Edzelf/ESP32-Radio/src/oled.h

//***************************************************************************************************
//                                   O L E D . H                                                    *
//***************************************************************************************************
// Driver for SSD1306/SSD1309/SH1106 display                                                        *
//***************************************************************************************************
// 25-02-2021, ES: Correct bug, isSH1106 was always set.                                            *
//***************************************************************************************************
#include <driver/i2c.h>
#include <string.h>

#define OLED_I2C_ADDRESS   0x3C
#define SCREEN_WIDTH        128                    // OLED display width, in pixels
#define SCREEN_HEIGHT        64                    // OLED display height, in pixels

// Color definitions.  OLED only have 2 colors.
#define BLACK   0
#define BLUE    0xFF
#define RED     0xFF
#define GREEN   0
#define CYAN    GREEN | BLUE
#define MAGENTA RED | BLUE
#define YELLOW  RED | GREEN
#define WHITE   RED | GREEN | BLUE

#define OLED_NPAG    8                             // Number of pages (text lines)

// Data to display.  There are TFTSECS sections
struct page_struct
{
  uint8_t   page[128] ;                            // Buffer for one page (8 pixels heigh)
  bool      dirty ;                                // True if modified
} ;
uint8_t     fillbuf[] = { 0, 0, 0, 0 } ;           // To clear 4 bytes of SH1106 RAM

class OLED
{
  public:
    OLED    ( uint8_t sda, uint8_t scl ) ;            // Constructor
    void      clear() ;                               // Clear buffer
    void      display() ;                             // Display buffer
    void      print ( char c ) ;                      // Print a character
    void      print ( const char* str ) ;             // Print a string
    void      setCursor ( uint8_t x, uint8_t y ) ;    // Position the cursor
    void      fillRect ( uint8_t x, uint8_t y,        // Fill a rectangle
                         uint8_t w, uint8_t h,
                         uint8_t color ) ;
    void      drawBitmap ( uint8_t x, uint8_t y,      // Bitmap to display buffer
                           uint8_t* buf,
                           uint8_t w,
                           uint8_t h ) ;        
  private:
    bool                    isSH1106 = false ;        // Display is a SH1106 or not
    bool                    isSSD1309 = false ;       // Display is a SSD1309 or not
    i2c_cmd_handle_t        i2Cchan ;                 // Channel for I2C communication
    struct page_struct*     ssdbuf = NULL ;
    const  uint8_t*         font ;                    // Font to use
    uint8_t                 xchar = 0 ;               // Current cursor position (text)
    uint8_t                 ychar = 0 ;               // Current cursor position (text)
    void                    openI2Cchan() ;           // Open I2C channel
    void                    closeI2Cchan() ;          // Close I2C channel
    void                    wrI2Cchan ( uint8_t b ) ; // Send 1 byte to I2C buffer
} ;


OLED* tft = NULL ;                                    // Object for display

#define TFTSECS 4
scrseg_struct     tftdata[TFTSECS] =                  // Screen divided in 3 segments + 1 overlay
{                                                     // One text line is 8 pixels
  { false, WHITE,   0,  8, "" },                      // 1 top line
  { false, CYAN,    8, 32, "" },                      // 4 lines in the middle
  { false, YELLOW, 40, 22, "" },                      // 3 lines at the bottom, leave room for indicator
  { false, GREEN,  40, 22, "" }                       // 3 lines at the bottom for rotary encoder
} ;

// Various macro's to mimic the ST7735 version of display functions
#define dsp_setRotation()                                          // Use standard landscape format
#define dsp_setTextSize(a)                                         // Set the text size
#define dsp_setTextColor(a)
#define dsp_print(a)            tft->print ( a )                   // Print a string 
#define dsp_println(a)          tft->print ( a ) ; \
                                tft->print ( '\n' )                // Print string plus newline
#define dsp_setCursor(a,b)      tft->setCursor ( a, b )            // Position the cursor
#define dsp_fillRect(a,b,c,d,e) tft->fillRect ( a, b, c, d, e )    // Fill a rectangle
#define dsp_erase()             tft->clear()                       // Clear the screen
#define dsp_getwidth()          128                                // Get width of screen
#define dsp_getheight()         64                                 // Get height of screen
#define dsp_update()            tft->display()                     // Updates to the physical screen
#define dsp_usesSPI()           false                              // Does not use SPI

bool dsp_begin()
{
  
  dbgprint ( "Init OLED, I2C pins %d,%d",
             ini_block.tft_sda_pin,
             ini_block.tft_scl_pin ) ;
  if ( ( ini_block.tft_sda_pin >= 0 ) &&
       ( ini_block.tft_scl_pin >= 0 ) )
  {
    tft = new OLED ( ini_block.tft_sda_pin,
                     ini_block.tft_scl_pin ) ;                    // Create an instant for TFT
  }
  else
  {
    dbgprint ( "Init LCD failed!" ) ;
    
  }
  return ( tft != NULL ) ;
}



// Control byte
#define OLED_CONTROL_BYTE_CMD_SINGLE    0x80
#define OLED_CONTROL_BYTE_CMD_STREAM    0x00
#define OLED_CONTROL_BYTE_DATA_STREAM   0x40

// Fundamental commands (pg.28)
#define OLED_CMD_SET_CONTRAST           0x81    // follow with 0x7F
#define OLED_CMD_DISPLAY_RAM            0xA4
#define OLED_CMD_DISPLAY_ALLON          0xA5
#define OLED_CMD_DISPLAY_NORMAL         0xA6
#define OLED_CMD_DISPLAY_INVERTED       0xA7
#define OLED_CMD_DISPLAY_OFF            0xAE
#define OLED_CMD_DISPLAY_ON             0xAF
#define OLED_CMD_SCROLL_OFF             0x2E

// Addressing Command Table (pg.30)
#define OLED_CMD_SET_MEMORY_ADDR_MODE   0x20    // follow with 0x00 = HORZ mode = Behave like a KS108 graphic LCD
#define OLED_CMD_SET_COLUMN_RANGE       0x21    // can be used only in HORZ/VERT mode - follow with 0x00 and 0x7F = COL127
#define OLED_CMD_SET_PAGE_RANGE         0x22    // can be used only in HORZ/VERT mode - follow with 0x00 and 0x07 = PAGE7
#define OLED_CMD_SET_PAGE_START_ADDR    0xB0    // Set page start address for page addressing mode
// Hardware Config (pg.31)
#define OLED_CMD_SET_DISPLAY_START_LINE 0x40
#define OLED_CMD_SET_SEGMENT_REMAP      0xA1    
#define OLED_CMD_SET_MUX_RATIO          0xA8    // follow with 0x3F = 64 MUX
#define OLED_CMD_SET_COM_SCAN_MODE      0xC8    // Mirror Y
#define OLED_CMD_SET_DISPLAY_OFFSET     0xD3    // follow with 0x00
#define OLED_CMD_SET_COM_PIN_MAP        0xDA    // follow with 0x12
#define OLED_CMD_NOP                    0xE3    // NOP

// Timing and Driving Scheme (pg.32)
#define OLED_CMD_SET_DISPLAY_CLK_DIV    0xD5    // follow with 0x80
#define OLED_CMD_SET_PRECHARGE          0xD9    // follow with 0xF1
#define OLED_CMD_SET_VCOMH_DESELCT      0xDB    // follow with 0x30

// Charge Pump (pg.62)
#define OLED_CMD_SET_CHARGE_PUMP        0x8D    // follow with 0x14

const uint8_t OLEDFONTWIDTH = 5 ;
const uint8_t OLEDfont[] =
            {
              0x00, 0x00, 0x00, 0x00, 0x00, // SPACE
              0x00, 0x00, 0x5F, 0x00, 0x00, // !
              0x00, 0x03, 0x00, 0x03, 0x00, // "
              0x14, 0x3E, 0x14, 0x3E, 0x14, // #
              0x24, 0x2A, 0x7F, 0x2A, 0x12, // $
              0x43, 0x33, 0x08, 0x66, 0x61, // %
              0x36, 0x49, 0x55, 0x22, 0x50, // &
              0x00, 0x05, 0x03, 0x00, 0x00, // '
              0x00, 0x1C, 0x22, 0x41, 0x00, // (
              0x00, 0x41, 0x22, 0x1C, 0x00, // )
              0x14, 0x08, 0x3E, 0x08, 0x14, // *
              0x08, 0x08, 0x3E, 0x08, 0x08, // +
              0x00, 0xA0, 0x60, 0x00, 0x00, // ,
              0x08, 0x08, 0x08, 0x08, 0x08, // -
              0x00, 0x60, 0x60, 0x00, 0x00, // .
              0x20, 0x10, 0x08, 0x04, 0x02, // /
            
              0x3E, 0x51, 0x49, 0x45, 0x3E, // 0
              0x00, 0x04, 0x02, 0x7F, 0x00, // 1
              0x42, 0x61, 0x51, 0x49, 0x46, // 2
              0x22, 0x41, 0x49, 0x49, 0x36, // 3
              0x18, 0x14, 0x12, 0x7F, 0x10, // 4
              0x27, 0x45, 0x45, 0x45, 0x39, // 5
              0x3E, 0x49, 0x49, 0x49, 0x32, // 6
              0x01, 0x01, 0x71, 0x09, 0x07, // 7
              0x36, 0x49, 0x49, 0x49, 0x36, // 8
              0x26, 0x49, 0x49, 0x49, 0x3E, // 9
              0x00, 0x36, 0x36, 0x00, 0x00, // :
              0x00, 0x56, 0x36, 0x00, 0x00, // ;
              0x08, 0x14, 0x22, 0x41, 0x00, // <
              0x14, 0x14, 0x14, 0x14, 0x14, // =
              0x00, 0x41, 0x22, 0x14, 0x08, // >
              0x02, 0x01, 0x51, 0x09, 0x06, // ?
            
              0x3E, 0x41, 0x59, 0x55, 0x5E, // @
              0x7E, 0x09, 0x09, 0x09, 0x7E, // A
              0x7F, 0x49, 0x49, 0x49, 0x36, // B
              0x3E, 0x41, 0x41, 0x41, 0x22, // C
              0x7F, 0x41, 0x41, 0x41, 0x3E, // D
              0x7F, 0x49, 0x49, 0x49, 0x41, // E
              0x7F, 0x09, 0x09, 0x09, 0x01, // F
              0x3E, 0x41, 0x41, 0x49, 0x3A, // G
              0x7F, 0x08, 0x08, 0x08, 0x7F, // H
              0x00, 0x41, 0x7F, 0x41, 0x00, // I
              0x30, 0x40, 0x40, 0x40, 0x3F, // J
              0x7F, 0x08, 0x14, 0x22, 0x41, // K
              0x7F, 0x40, 0x40, 0x40, 0x40, // L
              0x7F, 0x02, 0x0C, 0x02, 0x7F, // M
              0x7F, 0x02, 0x04, 0x08, 0x7F, // N
              0x3E, 0x41, 0x41, 0x41, 0x3E, // O
            
              0x7F, 0x09, 0x09, 0x09, 0x06, // P
              0x1E, 0x21, 0x21, 0x21, 0x5E, // Q
              0x7F, 0x09, 0x09, 0x09, 0x76, // R
              0x26, 0x49, 0x49, 0x49, 0x32, // S
              0x01, 0x01, 0x7F, 0x01, 0x01, // T
              0x3F, 0x40, 0x40, 0x40, 0x3F, // U
              0x1F, 0x20, 0x40, 0x20, 0x1F, // V
              0x7F, 0x20, 0x10, 0x20, 0x7F, // W
              0x41, 0x22, 0x1C, 0x22, 0x41, // X
              0x07, 0x08, 0x70, 0x08, 0x07, // Y
              0x61, 0x51, 0x49, 0x45, 0x43, // Z
              0x00, 0x7F, 0x41, 0x00, 0x00, // [
              0x02, 0x04, 0x08, 0x10, 0x20, // backslash
              0x00, 0x00, 0x41, 0x7F, 0x00, // ]
              0x04, 0x02, 0x01, 0x02, 0x04, // ^
              0x40, 0x40, 0x40, 0x40, 0x40, // _
            
              0x00, 0x01, 0x02, 0x04, 0x00, // `
              0x20, 0x54, 0x54, 0x54, 0x78, // a
              0x7F, 0x44, 0x44, 0x44, 0x38, // b
              0x38, 0x44, 0x44, 0x44, 0x44, // c
              0x38, 0x44, 0x44, 0x44, 0x7F, // d
              0x38, 0x54, 0x54, 0x54, 0x18, // e
              0x04, 0x04, 0x7E, 0x05, 0x05, // f
              0x18, 0xA4, 0xA4, 0xA4, 0x78, // g
              0x7F, 0x08, 0x04, 0x04, 0x78, // h
              0x00, 0x44, 0x7D, 0x40, 0x00, // i
              0x20, 0x40, 0x44, 0x3D, 0x00, // j
              0x7F, 0x10, 0x28, 0x44, 0x00, // k
              0x00, 0x41, 0x7F, 0x40, 0x00, // l
              0x7C, 0x04, 0x78, 0x04, 0x78, // m
              0x7C, 0x08, 0x04, 0x04, 0x78, // n
              0x38, 0x44, 0x44, 0x44, 0x38, // o
            
              0xFC, 0x24, 0x24, 0x24, 0x18, // p
              0x18, 0x24, 0x24, 0x24, 0xFC, // q
              0x00, 0x7C, 0x08, 0x04, 0x04, // r
              0x48, 0x54, 0x54, 0x54, 0x20, // s
              0x04, 0x04, 0x3F, 0x44, 0x44, // t
              0x3C, 0x40, 0x40, 0x20, 0x7C, // u
              0x1C, 0x20, 0x40, 0x20, 0x1C, // v
              0x3C, 0x40, 0x30, 0x40, 0x3C, // w
              0x44, 0x28, 0x10, 0x28, 0x44, // x
              0x0C, 0x50, 0x50, 0x50, 0x3C, // y
              0x44, 0x64, 0x54, 0x4C, 0x44, // z
              0x00, 0x08, 0x36, 0x41, 0x41, // {
              0x00, 0x00, 0x7F, 0x00, 0x00, // |
              0x41, 0x41, 0x36, 0x08, 0x00, // }
              0x02, 0x01, 0x02, 0x04, 0x02  // ~
            } ;


//***********************************************************************************************
//                                O L E D :: W R I 2 C C H A N                                  *
//***********************************************************************************************
// Write 1 byte to the I2C buffer.                                                              *
//***********************************************************************************************
void OLED::wrI2Cchan ( uint8_t b )                  // Send 1 byte to I2C buffer
{
  i2c_master_write_byte ( i2Cchan, b, true ) ;      // Add 1 byte to I2C buffer
}


//***********************************************************************************************
//                                O L E D :: O P E N I 2 C C H A N                              *
//***********************************************************************************************
// Open an I2c channel for communication.                                                       *
//***********************************************************************************************
void OLED::openI2Cchan()
{
  i2Cchan = i2c_cmd_link_create() ;                            // Create the link
  i2c_master_start ( i2Cchan ) ;                               // Start collecting data in buffer
  wrI2Cchan ( (OLED_I2C_ADDRESS << 1) | I2C_MASTER_WRITE ) ;   // Send I2C address and write bit
}


//***********************************************************************************************
//                                O L E D :: C L O S E I 2 C C H A N                            *
//***********************************************************************************************
// Seend buffer and close the I2c channel.                                                      *
//***********************************************************************************************
void OLED::closeI2Cchan()
{
  i2c_master_stop ( i2Cchan ) ;                           // Stop filling buffer
  i2c_master_cmd_begin ( I2C_NUM_0, i2Cchan,              // Start actual transfer
                         10 / portTICK_PERIOD_MS ) ;      // Time-out
  i2c_cmd_link_delete ( i2Cchan ) ;                       // Delete the link
}


//***********************************************************************************************
//                                      O L E D :: P R I N T                                    *
//***********************************************************************************************
// Put a character in the buffer.                                                               *
//***********************************************************************************************
void OLED::print ( char c )
{
  if ( ( c >= ' ' ) && ( c <= '~' ) )                    // Check the legal range
  {
    memcpy ( &ssdbuf[ychar].page[xchar],                 // Copy bytes for 1 character
             &font[(c-32)*OLEDFONTWIDTH],
             OLEDFONTWIDTH ) ;
    ssdbuf[ychar].dirty = true ;                         // Notice change
  }
  else if ( c == '\n' )                                  // New line?
  {
    xchar = SCREEN_WIDTH ;                               // Yes, force next line
  }
  xchar += ( OLEDFONTWIDTH + 1 ) ;                    // Move x cursor
  if ( xchar > ( SCREEN_WIDTH - OLEDFONTWIDTH ) )     // End of line?
  {
    xchar = 0 ;                                          // Yes, mimic CR
    ychar = ( ychar + 1 ) & 7 ;                          // And LF
  }
}


//***********************************************************************************************
//                                   O L E D :: P R I N T                                    *
//***********************************************************************************************
// Put a character in the buffer.                                                               *
//***********************************************************************************************
void OLED::print ( const char* str )
{
  while ( *str )                                // Print until delimeter
  {
    print ( *str ) ;                            // Print next character
    str++ ;
  }
}


//***********************************************************************************************
//                                OLED :: D R A W B I T M A P                             *
//***********************************************************************************************
// Copy a bitmap to the display buffer.                                                         *
//***********************************************************************************************
void OLED::drawBitmap ( uint8_t x, uint8_t y, uint8_t* buf, uint8_t w, uint8_t h )
{
  uint8_t  pg ;                                           // Page to fill
  uint8_t  pat ;                                          // Fill pattern
  uint8_t  xc, yc ;                                       // Running x and y in rectangle
  uint8_t* p ;                                            // Point into ssdbuf
  uint8_t* s = buf ;                                      // Byte in input buffer
  uint8_t  m = 0x80 ;                                     // Mask in input buffer
  
  for ( yc = y ; yc < ( y + h ) ; yc++ )                  // Loop vertically
  {
    pg = ( yc / 8 ) % OLED_NPAG ;                         // Page involved
    pat = 1 << ( yc & 7 ) ;                               // Bit involved
    p = ssdbuf[pg].page + x ;                             // Point to right place
    for ( xc = x ; xc < ( x + w ) ; xc++ )                // Loop horizontally
    {
      if ( *s & m )                                       // Set bit?
      {
        *p |= pat ;                                       // Yes, set bit
      }
      else
      {
        *p &= ~pat ;                                      // No, clear bit
      }
      p++ ;                                               // Next 8 pixels
      if ( ( m >>= 1 ) == 0 )                             // Shift input mask
      {
        m = 0x80 ;                                        // New byte
        s++ ;
      }
    }
    ssdbuf[pg].dirty = true ;                             // Page has been changed
  }
}


//***********************************************************************************************
//                                O L E D :: D I S P L A Y                                   *
//***********************************************************************************************
// Refresh the display.                                                                         *
//***********************************************************************************************
void OLED::display()
{
  uint8_t          pg ;                                       // Page number 0..OLED_NPAG - 1

  for ( pg = 0 ; pg < OLED_NPAG ; pg++ )
  {
    if ( ssdbuf[pg].dirty )                                   // Refresh needed?
    {
      ssdbuf[pg].dirty = false ;                              // Yes, set page to "up-to-date"
      openI2Cchan() ;                                         // Open I2C channel
      wrI2Cchan ( OLED_CONTROL_BYTE_CMD_SINGLE ) ;            // Set single byte command mode
      wrI2Cchan ( 0xB0 | pg ) ;                               // Set page address
      if ( isSH1106 || isSSD1309 )                            // Is it an SH1106 or SSD1309?
      {
        wrI2Cchan ( 0x00 ) ;                           	      // Set lower column address to 0
        wrI2Cchan ( 0x10 ) ;                                  // Set higher column address to 0
      }
      closeI2Cchan() ;                                        // Send and close I2C channel
      // Channel is closed and reopened because of limited buffer space
      openI2Cchan() ;                                         // Open I2C channel again
      wrI2Cchan ( OLED_CONTROL_BYTE_DATA_STREAM ) ;           // Set multi byte data mode
      if ( isSH1106 )                                         // Is it a SH1106?
      {
        i2c_master_write ( i2Cchan, fillbuf, 4, true ) ;      // Yes, fill extra RAM with zeroes
      }
      i2c_master_write ( i2Cchan, ssdbuf[pg].page, 128,       // Send 1 page with data
                         true ) ;
      closeI2Cchan() ;                                        // Send and close I2C channel
    }
  }
}


//***********************************************************************************************
//                                 O L E D :: C L E A R                                         *
//***********************************************************************************************
// Clear the display buffer and the display.                                                    *
//***********************************************************************************************
void OLED::clear()
{
  for ( uint8_t pg = 0 ; pg < OLED_NPAG ; pg++ )         // Handle all pages
  {
    memset ( ssdbuf[pg].page, BLACK, SCREEN_WIDTH ) ;    // Clears all pixels of 1 page
    ssdbuf[pg].dirty = true ;                            // Force refresh
  }
  xchar = 0 ;
  ychar = 0 ;
}


//***********************************************************************************************
//                                   O L E D :: S E T C U R S O R                               *
//***********************************************************************************************
// Position the cursor.  It will be set at a page boundary (line of texts).                     *
//***********************************************************************************************
void OLED::setCursor ( uint8_t x, uint8_t y )          // Position the cursor
{
  xchar = x % SCREEN_WIDTH ;
  ychar = y / 8 % OLED_NPAG ;
}


//***********************************************************************************************
//                                   O L E D :: F I L L R E C T                                 *
//***********************************************************************************************
// Fill a rectangle.  It will clear a number of pages (lines of texts ).                        *
// Not very fast....                                                                            *
//***********************************************************************************************
void OLED::fillRect ( uint8_t x, uint8_t y, uint8_t w, uint8_t h, uint8_t color )
{
  uint8_t  pg ;                                           // Page to fill
  uint8_t  pat ;                                          // Fill pattern
  uint8_t  xc, yc ;                                       // Running x and y in rectangle
  uint8_t* p ;                                            // Point into ssdbuf
  
  for ( yc = y ; yc < ( y + h ) ; yc++ )                  // Loop vertically
  {
    pg = ( yc / 8 ) % OLED_NPAG ;                         // Page involved
    pat = 1 << ( yc & 7 ) ;                               // Bit involved
    p = ssdbuf[pg].page + x ;                             // Point to right place
    for ( xc = x ; xc < ( x + w ) ; xc++ )                // Loop horizontally
    {
      if ( color )                                        // Set bit?
      {
        *p |= pat ;                                       // Yes, set bit
      }
      else
      {
        *p &= ~pat ;                                      // No, clear bit
      }
      p++ ;                                               // Next 8 pixels
    }
    ssdbuf[pg].dirty = true ;                             // Page has been changed
  }
}


//***********************************************************************************************
//                                O L E D constructor                                           *
//***********************************************************************************************
// Constructor for the display.                                                                 *
//***********************************************************************************************
OLED::OLED ( uint8_t sda, uint8_t scl )
{
  i2c_config_t   i2c_config =                                // Set-up of I2C configuration
    {
      I2C_MODE_MASTER, 
      (gpio_num_t)sda,                                       // Pull ups for sda and scl
      GPIO_PULLUP_ENABLE,
      (gpio_num_t)scl,
      GPIO_PULLUP_ENABLE,
      400000                                                 // High speed
    } ;
  uint8_t      initbuf[] =                                   // Initial commands to init OLED
                  {
                    OLED_CONTROL_BYTE_CMD_STREAM,            // Stream next bytes
                    OLED_CMD_DISPLAY_OFF,                    // Display off
                    OLED_CMD_SET_DISPLAY_CLK_DIV, 0x80,      // Set divide ratio
                    OLED_CMD_SET_MUX_RATIO, SCREEN_HEIGHT-1, // Set multiplex ration (1:HEIGHT)
                    OLED_CMD_SET_DISPLAY_OFFSET, 0,          // Set diplay offset to 0
                    OLED_CMD_SET_DISPLAY_START_LINE,         // Set start line address
                    OLED_CMD_SET_CHARGE_PUMP, 0x14,          // Enable charge pump
                    OLED_CMD_SET_MEMORY_ADDR_MODE, 0x00,     // Set horizontal addressing mode
                    OLED_CMD_SET_SEGMENT_REMAP,              // Mirror X
                    OLED_CMD_SET_COM_SCAN_MODE,              // Mirror Y
                    OLED_CMD_SET_COM_PIN_MAP, 0x12,          // Set com pins hardware config
                    OLED_CMD_SET_CONTRAST, 0xFF,             // Set contrast
                    OLED_CMD_SET_PRECHARGE, 0xF1,            // Set precharge period
                    OLED_CMD_SET_VCOMH_DESELCT, 0x20,        // Set VCOMH
                    OLED_CMD_DISPLAY_RAM,                    // Output followes RAM
                    OLED_CMD_DISPLAY_NORMAL,                 // Set normal color
                    OLED_CMD_SCROLL_OFF,                     // Stop scrolling
                    OLED_CMD_DISPLAY_ON                      // Display on
                  } ;
  #if defined ( OLED1106 )                                      // Is it an SH1106?
    isSH1106 = true ;                                           // Set display type                         
  #endif
  dbgprint ( "ISSH116 is %d", (int)isSH1106 ) ;
  #if defined ( OLED1309 )                                      // Is it an SSD1309?
    isSSD1309 = true ;                                          // Set display type                         
  #endif
  dbgprint ( "ISSSD1309 is %d", (int)isSSD1309 ) ;
  ssdbuf = (page_struct*) malloc ( 8 * sizeof(page_struct) ) ;  // Create buffer for screen
  font = OLEDfont ;
  i2c_param_config ( I2C_NUM_0, &i2c_config ) ;
  i2c_driver_install ( I2C_NUM_0, I2C_MODE_MASTER, 0, 0, 0 ) ;
  openI2Cchan() ;                                               // Open I2C channel
  i2c_master_write (  i2Cchan, initbuf, sizeof(initbuf),
                      true ) ;
  closeI2Cchan() ;                                              // Send and close I2C channel
  clear() ;                                                     // Clear the display
}


//**************************************************************************************************
//                                      D I S P L A Y B A T T E R Y                                *
//**************************************************************************************************
// Show the current battery charge level on the screen.                                            *
// It will overwrite the top divider.                                                              *
// No action if bat0/bat100 not defined in the preferences.                                        *
//**************************************************************************************************
void displaybattery()
{
  if ( tft )
  {
    if ( ini_block.bat0 < ini_block.bat100 )              // Levels set in preferences?
    {
      static uint16_t oldpos = 0 ;                        // Previous charge level
      uint16_t        ypos ;                              // Position on screen
      uint16_t        v ;                                 // Constrainted ADC value
      uint16_t        newpos ;                            // Current setting

      v = constrain ( adcval, ini_block.bat0,             // Prevent out of scale
                      ini_block.bat100 ) ;
      newpos = map ( v, ini_block.bat0,                   // Compute length of green bar
                     ini_block.bat100,
                     0, dsp_getwidth() ) ;
      if ( newpos != oldpos )                             // Value changed?
      {
        oldpos = newpos ;                                 // Remember for next compare
        ypos = tftdata[1].y - 5 ;                         // Just before 1st divider
        dsp_fillRect ( 0, ypos, newpos, 2, GREEN ) ;      // Paint green part
        dsp_fillRect ( newpos, ypos,
                       dsp_getwidth() - newpos,
                       2, RED ) ;                          // Paint red part
      }
    }
  }
}


//**************************************************************************************************
//                                      D I S P L A Y V O L U M E                                  *
//**************************************************************************************************
// Show the current volume as an indicator on the screen.                                          *
// The indicator is 2 pixels heigh.                                                                *
//**************************************************************************************************
void displayvolume()
{
  if ( tft )
  {
    static uint8_t oldvol = 0 ;                         // Previous volume
    uint8_t        newvol ;                             // Current setting
    uint16_t       pos ;                                // Positon of volume indicator

    newvol = vs1053player->getVolume() ;                // Get current volume setting
    if ( newvol != oldvol )                             // Volume changed?
    {
      oldvol = newvol ;                                 // Remember for next compare
      pos = map ( newvol, 0, 100, 0, dsp_getwidth() ) ; // Compute position on TFT
      dsp_fillRect ( 0, dsp_getheight() - 2,
                     pos, 2, RED ) ;                    // Paint red part
      dsp_fillRect ( pos, dsp_getheight() - 2,
                     dsp_getwidth() - pos, 2, GREEN ) ; // Paint green part
    }
  }
}


//**************************************************************************************************
//                                      D I S P L A Y T I M E                                      *
//**************************************************************************************************
// Show the time on the LCD at a fixed position in a specified color                               *
// To prevent flickering, only the changed part of the timestring is displayed.                    *
// An empty string will force a refresh on next call.                                              *
// A character on the screen is 8 pixels high and 6 pixels wide.                                   *
//**************************************************************************************************
void displaytime ( const char* str, uint16_t color )
{
  static char oldstr[9] = "........" ;             // For compare
  uint8_t     i ;                                  // Index in strings
  uint16_t    pos = dsp_getwidth() + TIMEPOS ;     // X-position of character, TIMEPOS is negative

  if ( str[0] == '\0' )                            // Empty string?
  {
    for ( i = 0 ; i < 8 ; i++ )                    // Set oldstr to dots
    {
      oldstr[i] = '.' ;
    }
    return ;                                       // No actual display yet
  }
  if ( tft )                                       // TFT active?
  {
    dsp_setTextColor ( color ) ;                   // Set the requested color
    for ( i = 0 ; i < 8 ; i++ )                    // Compare old and new
    {
      if ( str[i] != oldstr[i] )                   // Difference?
      {
        dsp_fillRect ( pos, 0, 6, 8, BLACK ) ;     // Clear the space for new character
        dsp_setCursor ( pos, 0 ) ;                 // Prepare to show the info
        dsp_print ( str[i] ) ;                     // Show the character
        oldstr[i] = str[i] ;                       // Remember for next compare
      }
      pos += 6 ;                                   // Next position
    }
  }
}
