Edzelf/ESP32-Radio/ESP32-Radio.ino

// ESP32-Radio.ino
//
// This is just a wrapper for the Arduino IDE version of ESP32-Radio.
// ESP32-Radio is designed to be compiled in the PlatformIO IDE.
// main.cpp will be compiled and linked automatically by the Arduino IDE.
// main.cpp contains the setup() and the loop() functions required for the Arduino environment.
//
// 21-09-2020, ES
//
