Edzelf/ESP32-Radio/src/favicon_ico.h

// favicon.ico file in raw data format for PROGMEM
//
const uint8_t favicon_ico[] PROGMEM = {
0x00, 0x00, 0x01, 0x00, 0x01, 0x00, 0x20, 0x20, 0x10, 0x00, 0x00, 0x00, 0x00, 0x00, 0xe8, 0x02,
0x00, 0x00, 0x16, 0x00, 0x00, 0x00, 0x28, 0x00, 0x00, 0x00, 0x20, 0x00, 0x00, 0x00, 0x40, 0x00,
0x00, 0x00, 0x01, 0x00, 0x04, 0x00, 0x00, 0x00, 0x00, 0x00, 0x80, 0x02, 0x00, 0x00, 0x00, 0x00,
0x00, 0x00, 0x00, 0x00, 0x00, 0x00, 0x00, 0x00, 0x00, 0x00, 0x00, 0x00, 0x00, 0x00, 0x00, 0x00,
0x00, 0x00, 0x00, 0x00, 0x80, 0x00, 0x00, 0x80, 0x00, 0x00, 0x00, 0x80, 0x80, 0x00, 0x80, 0x00,
0x00, 0x00, 0x80, 0x00, 0x80, 0x00, 0x80, 0x80, 0x00, 0x00, 0x80, 0x80, 0x80, 0x00, 0xc0, 0xc0,
0xc0, 0x00, 0x00, 0x00, 0xff, 0x00, 0x00, 0xff, 0x00, 0x00, 0x00, 0xff, 0xff, 0x00, 0xff, 0x00,
0x00, 0x00, 0xff, 0x00, 0xff, 0x00, 0xff, 0xff, 0x00, 0x00, 0xff, 0xff, 0xff, 0x00, 0x66, 0x66,
0x66, 0x66, 0x66, 0x66, 0x66, 0x66, 0x66, 0x66, 0x66, 0x66, 0x66, 0x66, 0x66, 0x66, 0x66, 0x66,
0x66, 0x66, 0x66, 0x66, 0x66, 0x66, 0x66, 0x66, 0x66, 0x66, 0x66, 0x66, 0x66, 0x66, 0x66, 0x66,
0x66, 0x66, 0x66, 0x66, 0x66, 0x66, 0x66, 0x66, 0x66, 0x66, 0x66, 0x66, 0x66, 0x66, 0x66, 0x66,
0x66, 0x66, 0x66, 0x66, 0x66, 0x66, 0x66, 0x66, 0x66, 0x66, 0x66, 0x66, 0x66, 0x66, 0x66, 0x66,
0x66, 0x66, 0x66, 0x66, 0x66, 0x66, 0x66, 0x66, 0x66, 0x66, 0x66, 0x66, 0x66, 0x66, 0x66, 0x66,
0x66, 0x66, 0x66, 0x66, 0x66, 0x66, 0x66, 0x66, 0x66, 0x66, 0x66, 0x66, 0x66, 0x66, 0x66, 0x66,
0x66, 0x66, 0x66, 0x66, 0x66, 0x66, 0x66, 0x66, 0x66, 0x66, 0x66, 0x66, 0x66, 0x66, 0x64, 0xe2,
0x64, 0xe6, 0x4e, 0xe6, 0xe2, 0x66, 0xee, 0x6e, 0x24, 0xe2, 0x66, 0xee, 0xe2, 0x66, 0x64, 0xe2,
0x66, 0xe0, 0xee, 0x06, 0xe2, 0x4e, 0x20, 0xee, 0x24, 0xe2, 0x4e, 0x26, 0x6e, 0x66, 0x64, 0xe2,
0x4e, 0x20, 0x6e, 0x06, 0xe2, 0x6e, 0x00, 0x6e, 0x24, 0xe2, 0x6e, 0x66, 0x4e, 0x26, 0x64, 0xee,
0xee, 0x20, 0x04, 0xee, 0xe2, 0x6e, 0x00, 0x6e, 0x24, 0xe2, 0x6e, 0x66, 0x4e, 0x26, 0x64, 0xe2,
0x06, 0xe2, 0x66, 0x06, 0xe6, 0x6e, 0x20, 0xee, 0x24, 0xe2, 0x4e, 0x26, 0x6e, 0x26, 0x64, 0xe2,
0x04, 0xe2, 0x6e, 0xee, 0x66, 0x66, 0xee, 0x6e, 0x24, 0xe2, 0x66, 0xee, 0xe2, 0x66, 0x64, 0xe2,
0x06, 0xe2, 0x66, 0x66, 0x66, 0x66, 0x66, 0x6e, 0x26, 0x66, 0x66, 0x66, 0x66, 0x66, 0x64, 0xee,
0xee, 0x66, 0x66, 0x66, 0x66, 0x66, 0x66, 0x6e, 0x24, 0xe2, 0x66, 0x66, 0x66, 0x66, 0x66, 0x66,
0x66, 0x66, 0x66, 0x66, 0x66, 0x66, 0x66, 0x66, 0x66, 0x66, 0x66, 0x66, 0x66, 0x66, 0x66, 0x66,
0x66, 0x66, 0x66, 0x66, 0x66, 0x66, 0x66, 0x66, 0x66, 0x66, 0x66, 0x66, 0x66, 0x66, 0x66, 0x66,
0x66, 0x66, 0x66, 0x66, 0x66, 0x66, 0x66, 0x66, 0x66, 0x66, 0x66, 0x66, 0x66, 0x66, 0x66, 0x66,
0x66, 0x66, 0x66, 0x66, 0x66, 0x66, 0x66, 0x66, 0x66, 0x66, 0x66, 0x66, 0x66, 0x66, 0x66, 0x64,
0xee, 0xee, 0xee, 0x26, 0x66, 0xee, 0xee, 0x66, 0x4e, 0x66, 0x66, 0x66, 0x66, 0x66, 0x66, 0x64,
0xe6, 0x66, 0x66, 0x66, 0x6e, 0x66, 0x6e, 0xe6, 0x4e, 0x66, 0x66, 0x66, 0x66, 0x66, 0x66, 0x64,
0xe6, 0x66, 0x66, 0x66, 0x66, 0x66, 0x66, 0xe2, 0x4e, 0x66, 0x66, 0x66, 0x66, 0x66, 0x66, 0x64,
0xe6, 0x66, 0x66, 0x66, 0x66, 0x66, 0x0e, 0xe6, 0x4e, 0x66, 0x66, 0x66, 0x66, 0x66, 0x66, 0x64,
0xe6, 0x66, 0x66, 0x66, 0x66, 0x0e, 0xee, 0x66, 0x4e, 0xee, 0xee, 0xe6, 0x66, 0x66, 0x66, 0x64,
0xee, 0xee, 0xe6, 0x66, 0x66, 0xee, 0x66, 0x66, 0x4e, 0x66, 0x64, 0xee, 0x66, 0x66, 0x66, 0x64,
0xe6, 0x66, 0x66, 0x66, 0x4e, 0xe6, 0x66, 0x66, 0x4e, 0x66, 0x66, 0x6e, 0x26, 0x66, 0x66, 0x64,
0xe6, 0x66, 0x66, 0x66, 0x4e, 0x66, 0x66, 0x66, 0x4e, 0x66, 0x66, 0x6e, 0x26, 0x66, 0x66, 0x64,
0xe6, 0x66, 0x66, 0x66, 0x0e, 0xe6, 0x4e, 0x66, 0x4e, 0x66, 0x64, 0xee, 0x66, 0x66, 0x66, 0x64,
0xee, 0xee, 0xee, 0x66, 0x64, 0xee, 0xee, 0x66, 0x4e, 0xee, 0xee, 0xe6, 0x66, 0x66, 0x66, 0x66,
0x66, 0x66, 0x66, 0x66, 0x66, 0x66, 0x66, 0x66, 0x66, 0x66, 0x66, 0x66, 0x66, 0x66, 0x66, 0x66,
0x66, 0x66, 0x66, 0x66, 0x66, 0x66, 0x66, 0x66, 0x66, 0x66, 0x66, 0x66, 0x66, 0x66, 0x66, 0x66,
0x66, 0x66, 0x66, 0x66, 0x66, 0x66, 0x66, 0x66, 0x66, 0x66, 0x66, 0x66, 0x66, 0x66, 0x00, 0x00,
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
} ;
